Super87380/custom-keyboard/Images/Case/centering_and_right_size.png

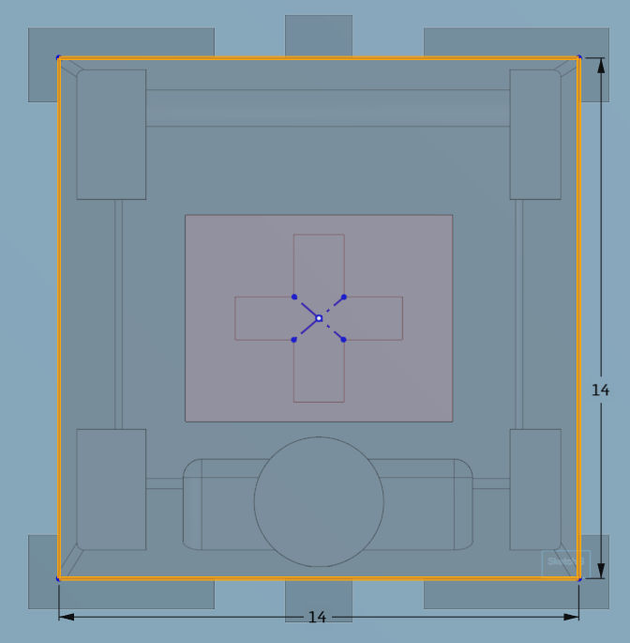
Images/Case/centering_and_right_size.png
