Super87380/custom-keyboard/Images/Case/plate_everything_cutout.png

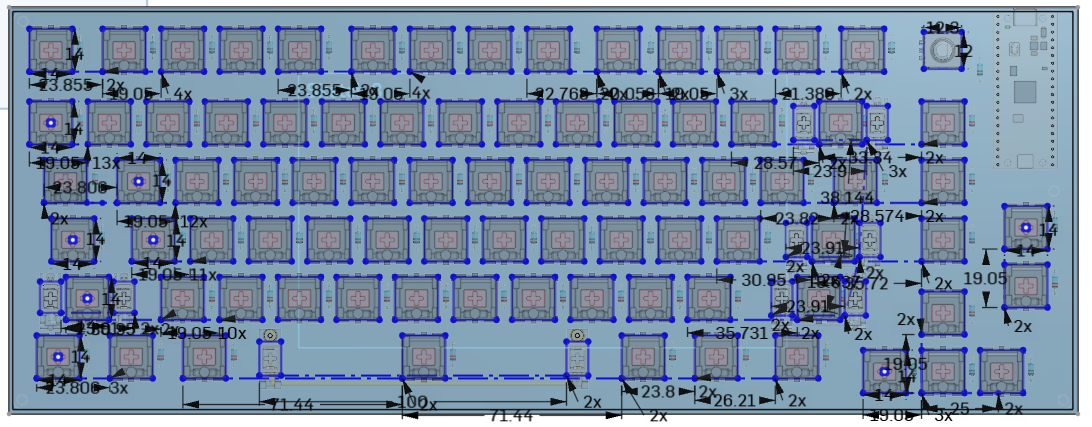
Images/Case/plate_everything_cutout.png
