Super87380/custom-keyboard/Images/Case/plate_finished.png

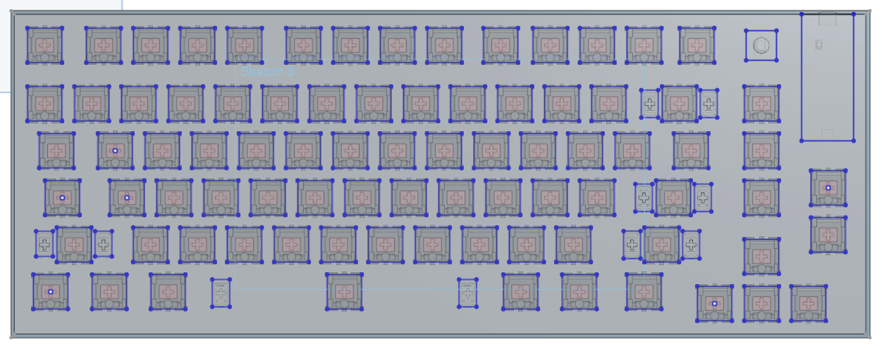
Images/Case/plate_finished.png
