Super87380/custom-keyboard/Images/Case/plate_switches_done.png

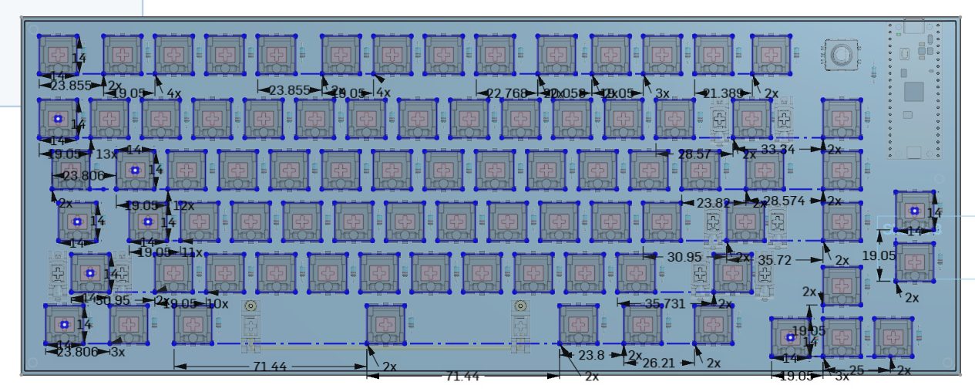
Images/Case/plate_switches_done.png
