Super87380/custom-keyboard/Images/Case/using_linear_pattern_tool.png

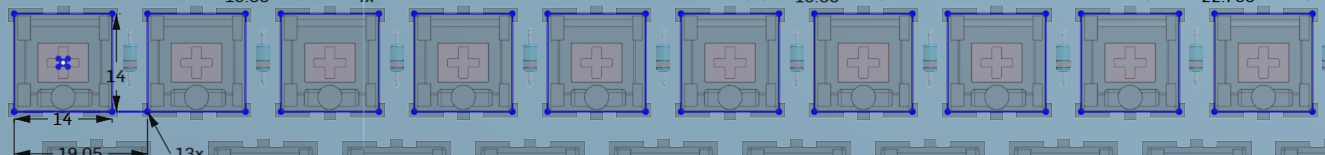
Images/Case/using_linear_pattern_tool.png
