Super87380/custom-keyboard/Images/Silk_Screen/Assets/flag-orpheus-top-bw (1).png

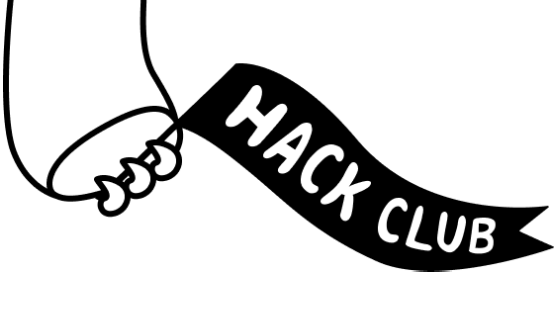
Images/Silk_Screen/Assets/flag-orpheus-top-bw (1).png
